agkrut/FPGA-Connect4-EE354-Final/pcb.sch

## EAGLE design pcb.sch (2019-04-19)

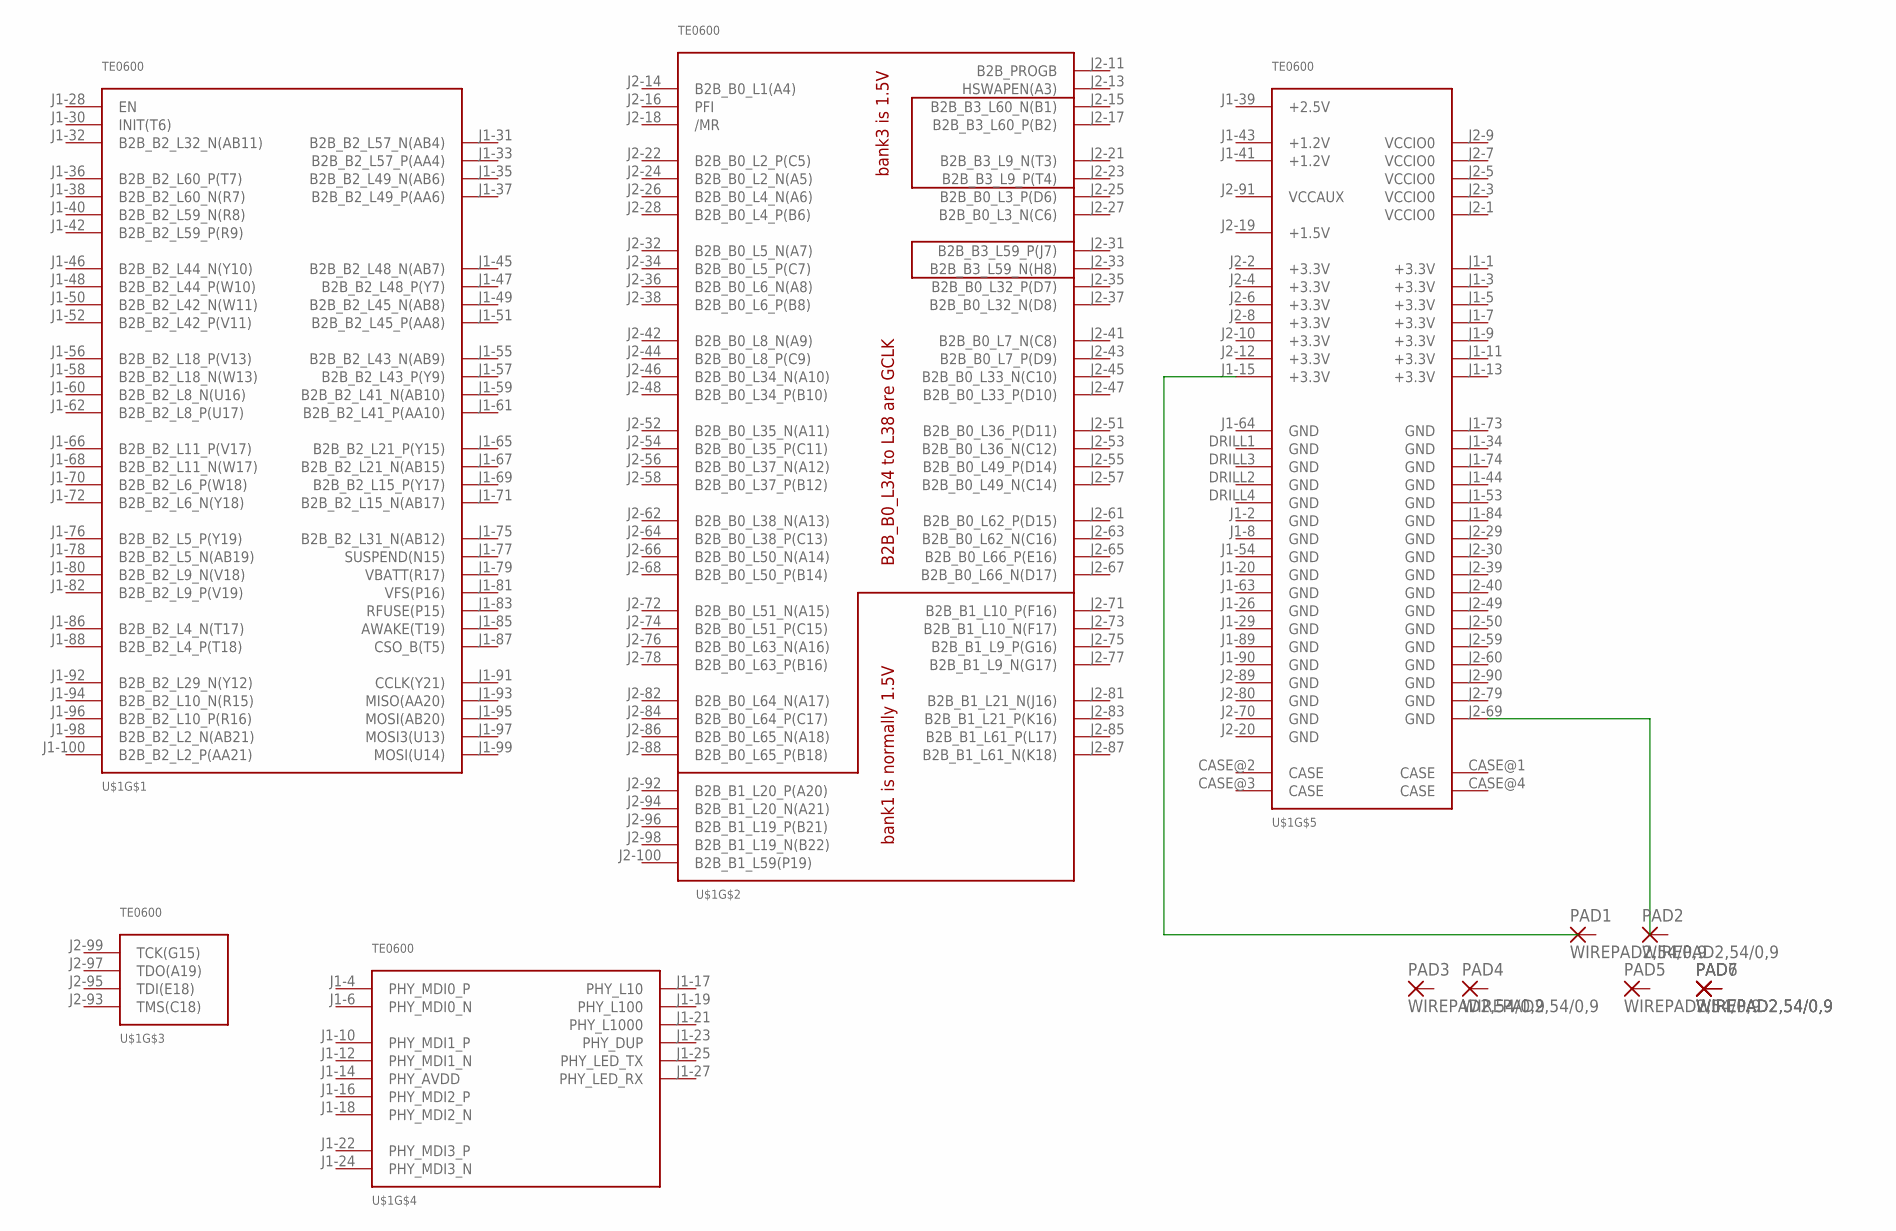
[picture p3: schematic pcb.sch]

Parts:
PAD1, PAD2, PAD3, PAD4, PAD5, PAD6, PAD7: WIREPAD2,54/0,9; 2,54/0,9
U$1: TE0600

Connections:
GND@30: U$1.J2-69 (GND)
unnamed: PAD6.1, PAD7.1
